lemonyzer/Projekt07/documentation/Bilder/Bauphase/1_pics_leds/pic_leds (4).jpg

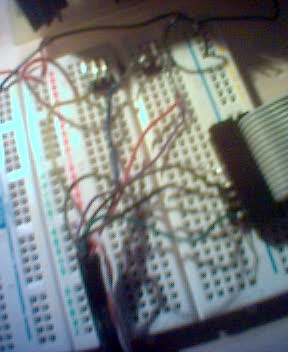
documentation/Bilder/Bauphase/1_pics_leds/pic_leds (4).jpg
