lemonyzer/Projekt07/documentation/Bilder/Bauphase/1_pics_leds/pic_leds.jpg

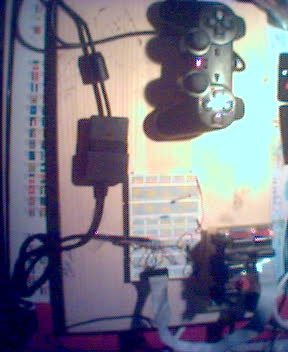
documentation/Bilder/Bauphase/1_pics_leds/pic_leds.jpg
