lemonyzer/Projekt07/documentation/Bilder/Bauphase/2_steckplatine/max_1 (5).jpg

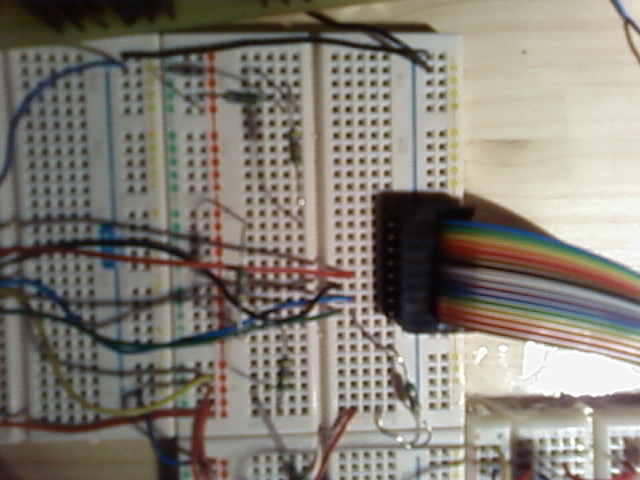
documentation/Bilder/Bauphase/2_steckplatine/max_1 (5).jpg
