lemonyzer/Projekt07/documentation/Bilder/Bauphase/2_steckplatine/max_1.jpg

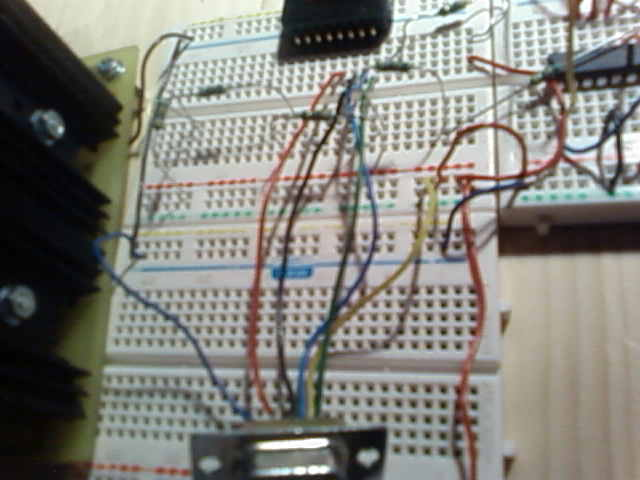
documentation/Bilder/Bauphase/2_steckplatine/max_1.jpg
