lemonyzer/Projekt07/documentation/Bilder/Bauphase/3_lochraster/PICT0151.JPG

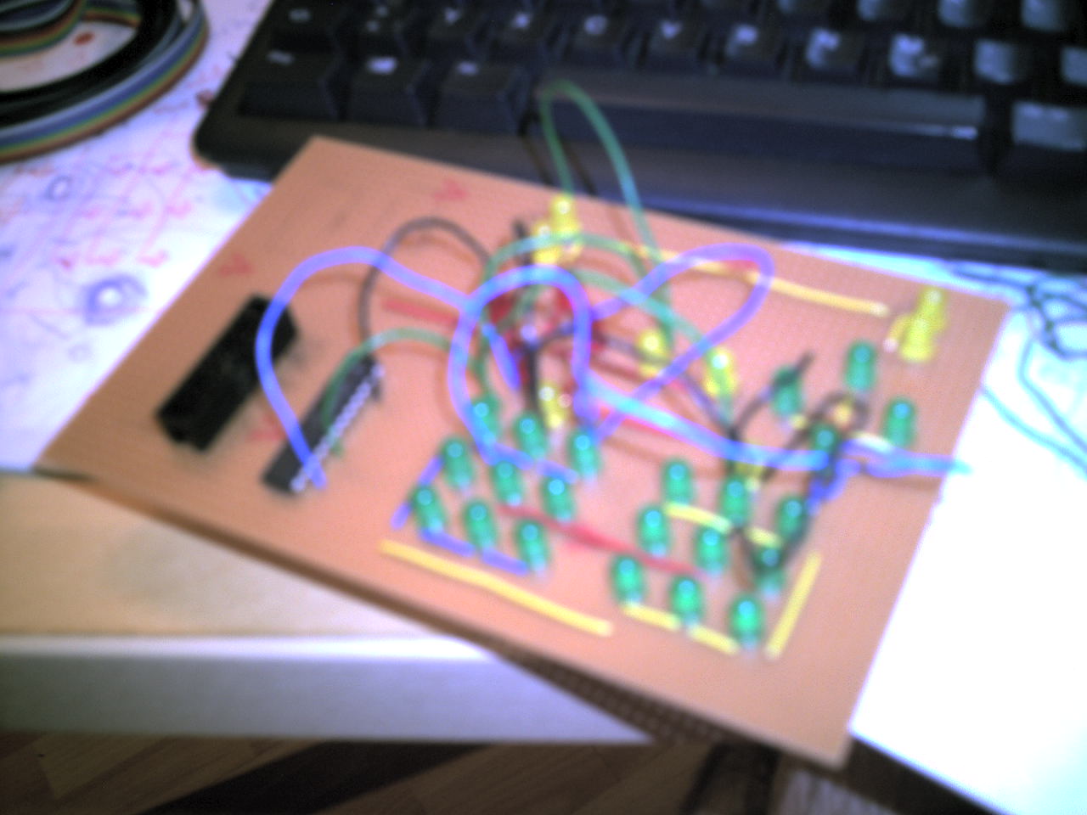
documentation/Bilder/Bauphase/3_lochraster/PICT0151.JPG
