lemonyzer/Projekt07/documentation/Bilder/Bauphase/3_lochraster/PICT0166.JPG

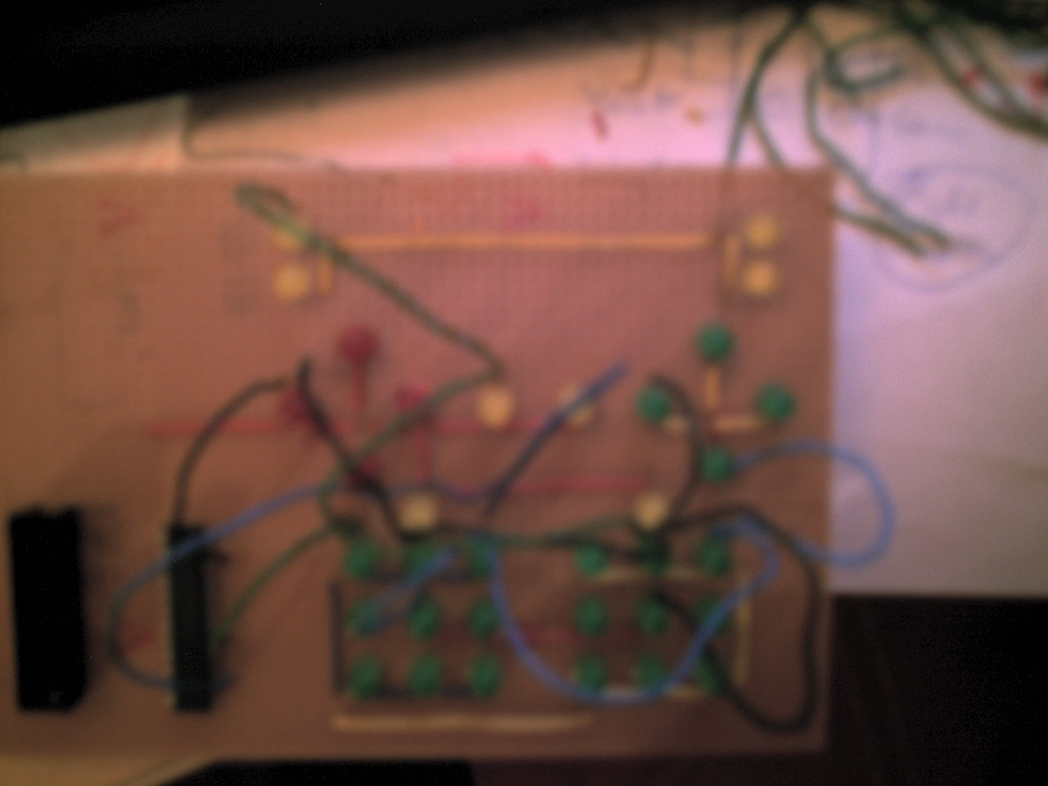
documentation/Bilder/Bauphase/3_lochraster/PICT0166.JPG
