lemonyzer/Projekt07/documentation/Bilder/fertig/1_steckplatine/steckplatine.jpg

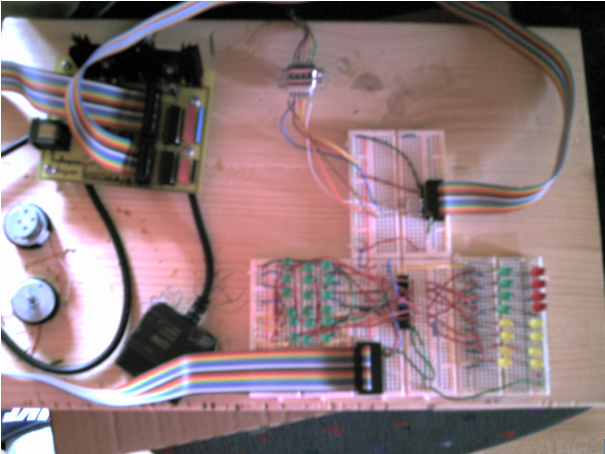
documentation/Bilder/fertig/1_steckplatine/steckplatine.jpg
