lemonyzer/Projekt07/documentation/Bilder/fertig/platine_funktioniert_nicht/PICT0186.JPG

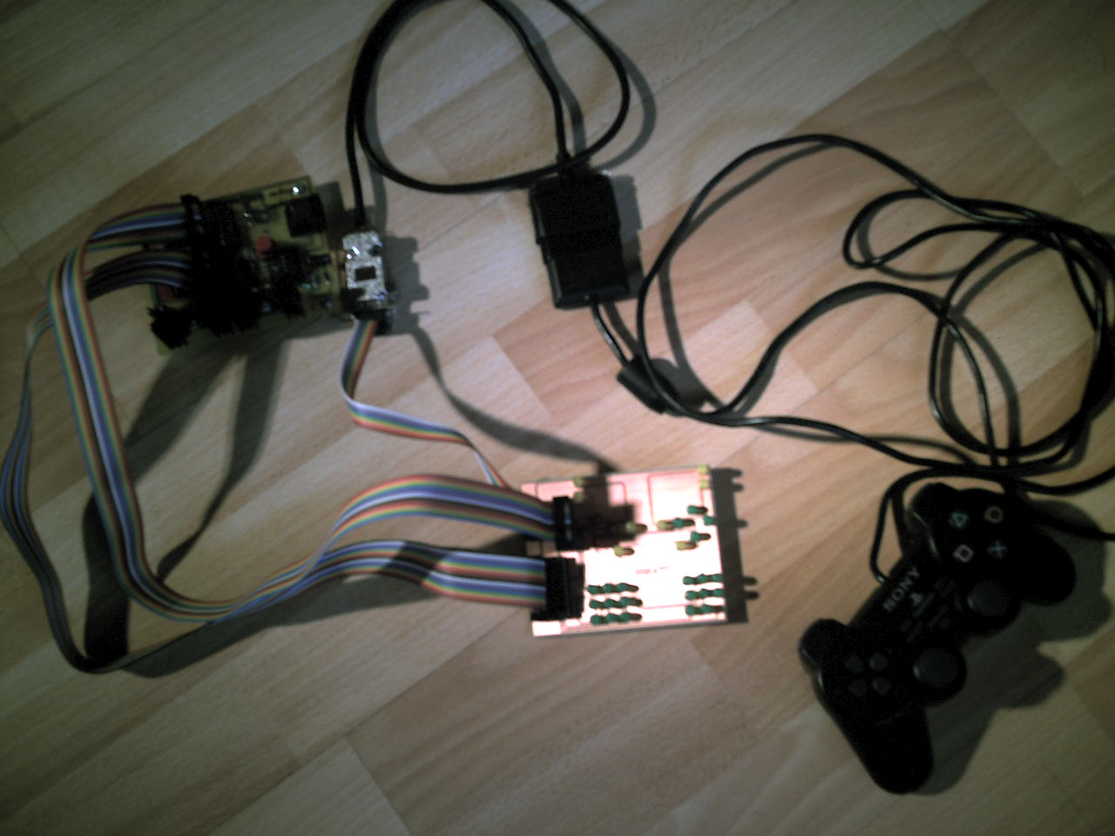
documentation/Bilder/fertig/platine_funktioniert_nicht/PICT0186.JPG
