lemonyzer/Projekt07/pics/Bild(35).jpg

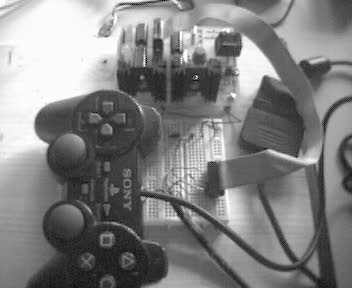
pics/Bild(35).jpg
