lemonyzer/Projekt07/pics/Bild_1.jpg

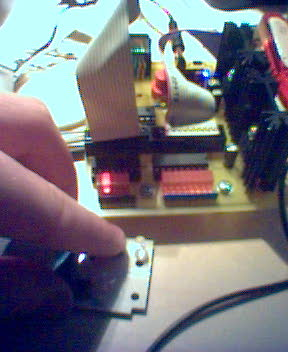
pics/Bild_1.jpg
