lemonyzer/Projekt07/pics/Bild_6.jpg

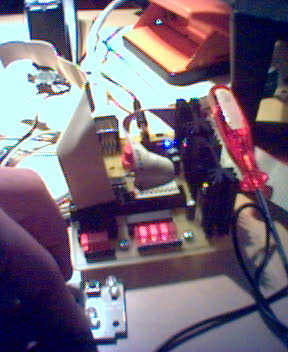
pics/Bild_6.jpg
